kanpapa/MC68EZ328/Pictures/dragonone_mt4lc4m16r6.jpg

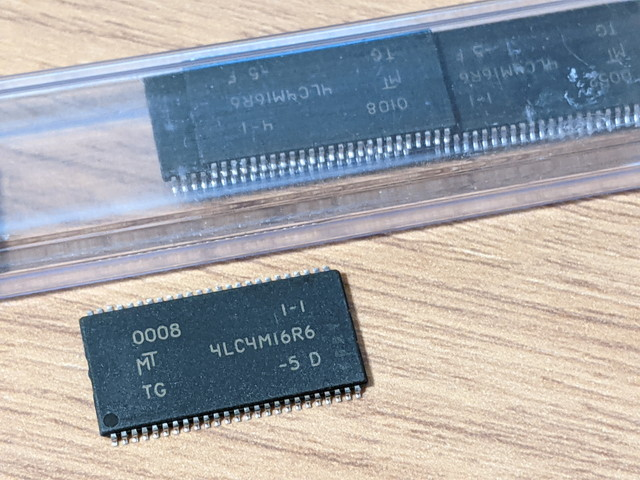
Pictures/dragonone_mt4lc4m16r6.jpg
