kanpapa/MC68EZ328/Pictures/dragonone_rev03_2021-09-16_063345.png

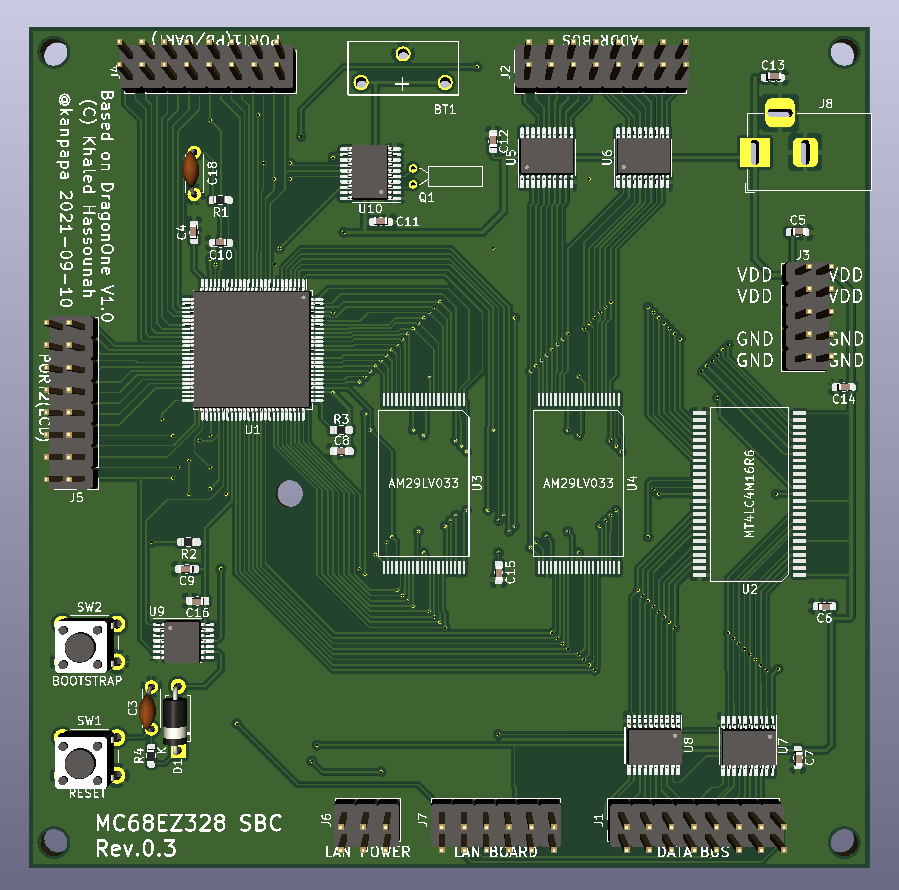
Pictures/dragonone_rev03_2021-09-16_063345.png
