kanpapa/MC68EZ328/Pictures/mc68ez328_sbc_lan_rev01_kicad.jpg

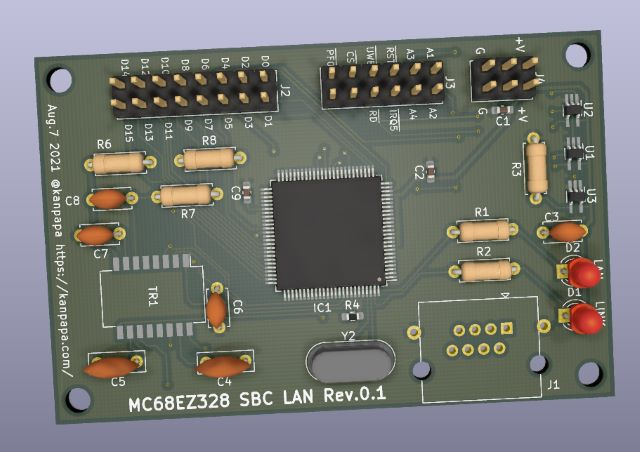
Pictures/mc68ez328_sbc_lan_rev01_kicad.jpg
