kanpapa/MC68EZ328/Pictures/dragonone_sbc_solder_pcb4.jpg

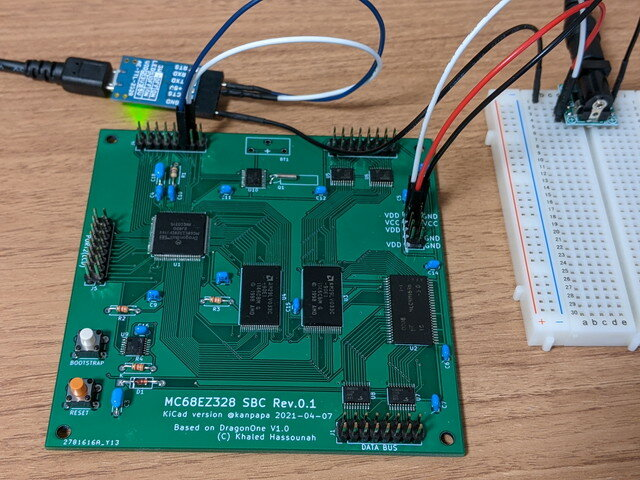
Pictures/dragonone_sbc_solder_pcb4.jpg
